lukeslaboratory/Stablebot-Core/STL's/Rear Z Plastic Peice.stl

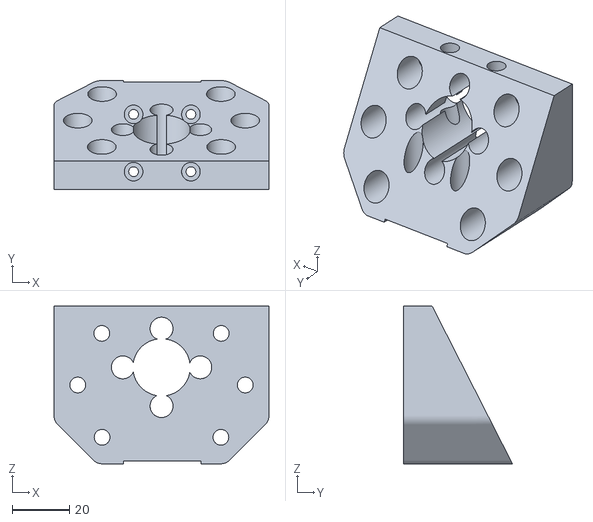
[picture p15: CAD file, 2021-12-18]
STL's/Rear Z Plastic Peice.stl
75.0 x 38.0 x 55.0
