lukeslaboratory/Stablebot-Core/STL's/Component449.3mf

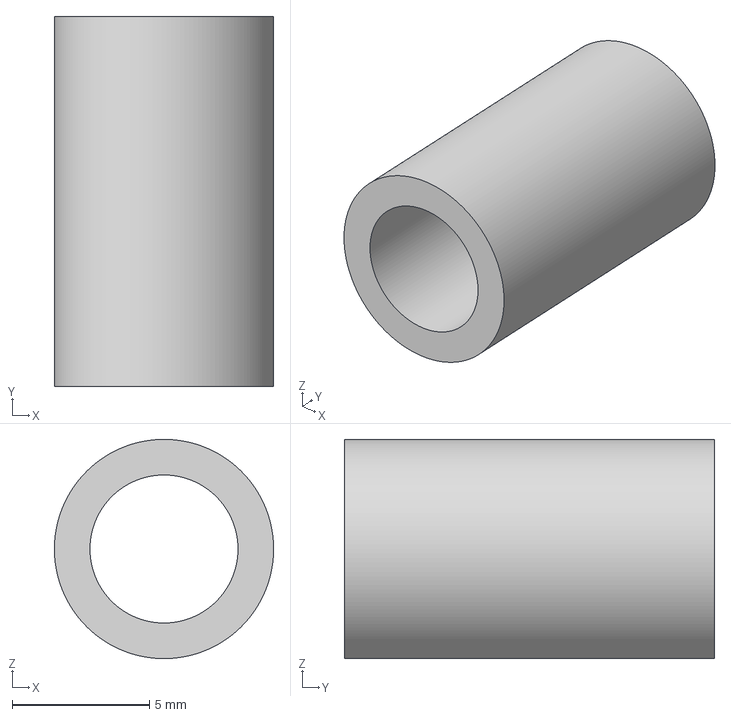
[picture p16: CAD file, 2021-12-18]
STL's/Component449.3mf
8.00 x 13.5 x 8.00 mm
