lukeslaboratory/Stablebot-Core/STL's/ToolPostBase.3mf

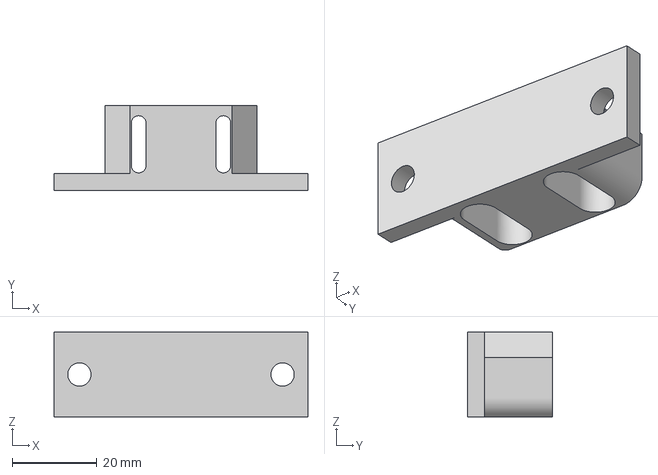
[picture p17: CAD file, 2021-12-18]
STL's/ToolPostBase.3mf
60.0 x 20.0 x 20.0 mm
