lukeslaboratory/Stablebot-Core/STL's/Plastic Base.3mf

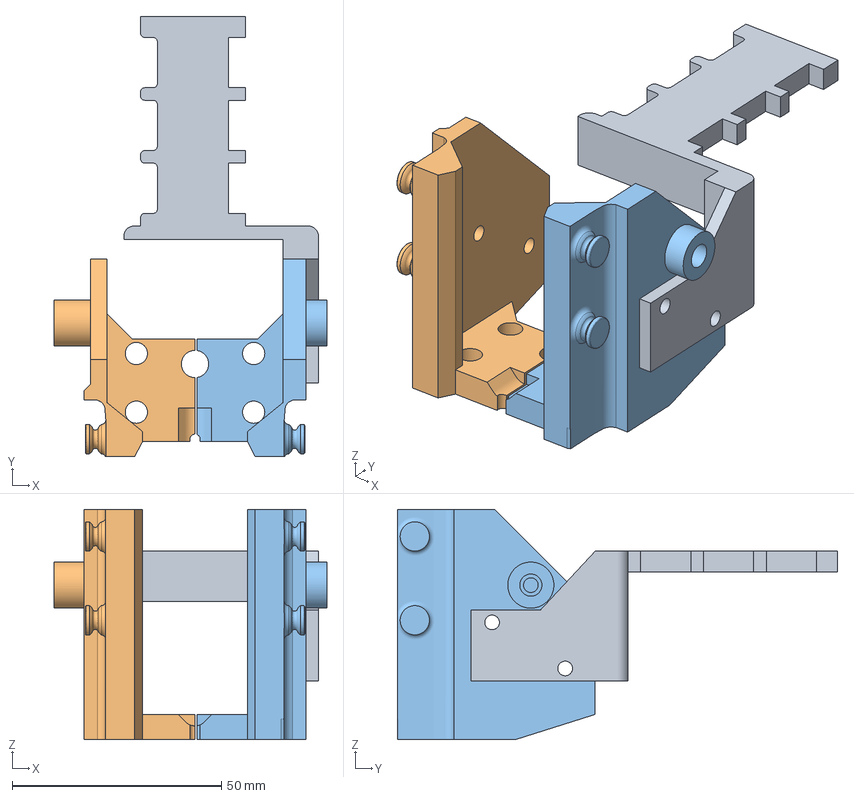
[picture p18: CAD file, 2021-12-18]
STL's/Plastic Base.3mf
65.2 x 105.0 x 55.0 mm
