lukeslaboratory/Stablebot-Core/STL's/Double_Shear_Rear.stl

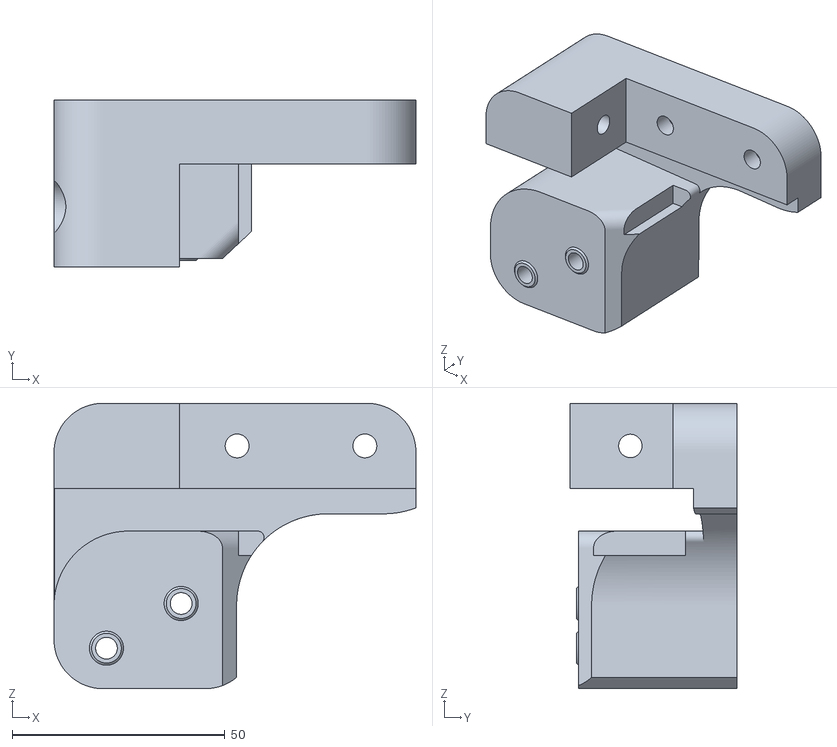
[picture p19: CAD file, 2021-12-18]
STL's/Double_Shear_Rear.stl
85.0 x 39.1 x 67.0
