lukeslaboratory/Stablebot-Core/STL's/Back Plate.3mf

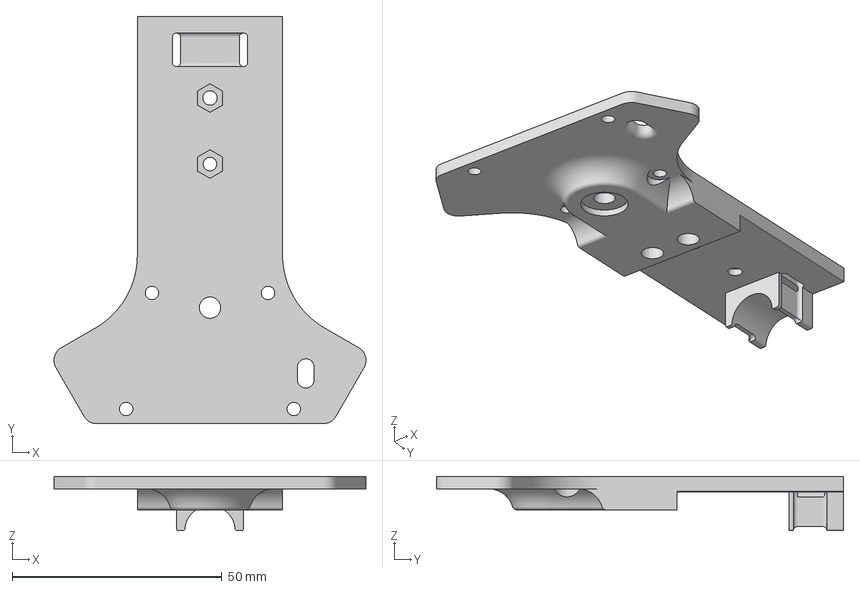
[picture p20: CAD file, 2021-12-18]
STL's/Back Plate.3mf
74.4 x 97.2 x 13.0 mm
