lukeslaboratory/Stablebot-Core/STL's/Belt_Motor_Tensioner.stl

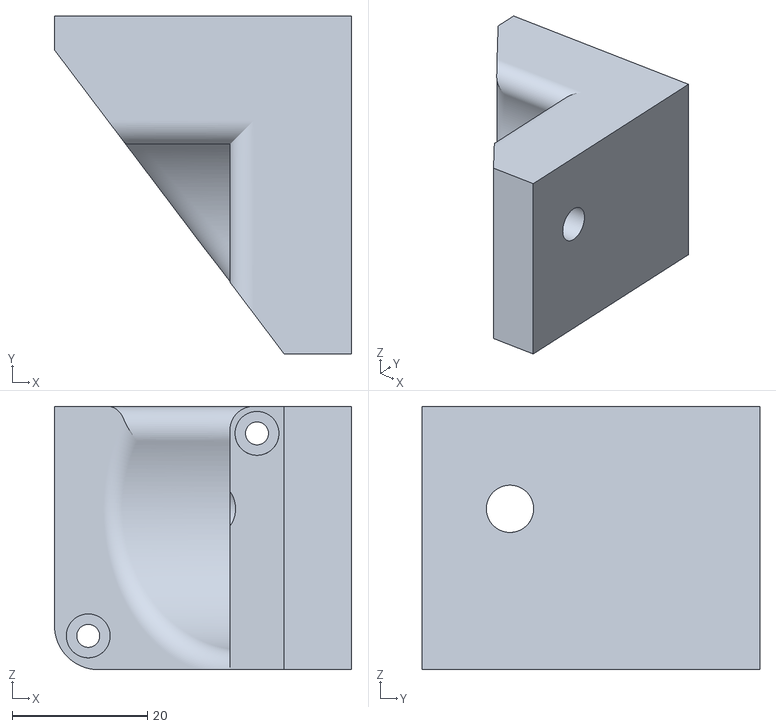
[picture p21: CAD file, 2021-12-18]
STL's/Belt_Motor_Tensioner.stl
44.0 x 50.0 x 39.0
