lukeslaboratory/Stablebot-Core/STL's/DoubleShear(Mirror).stl

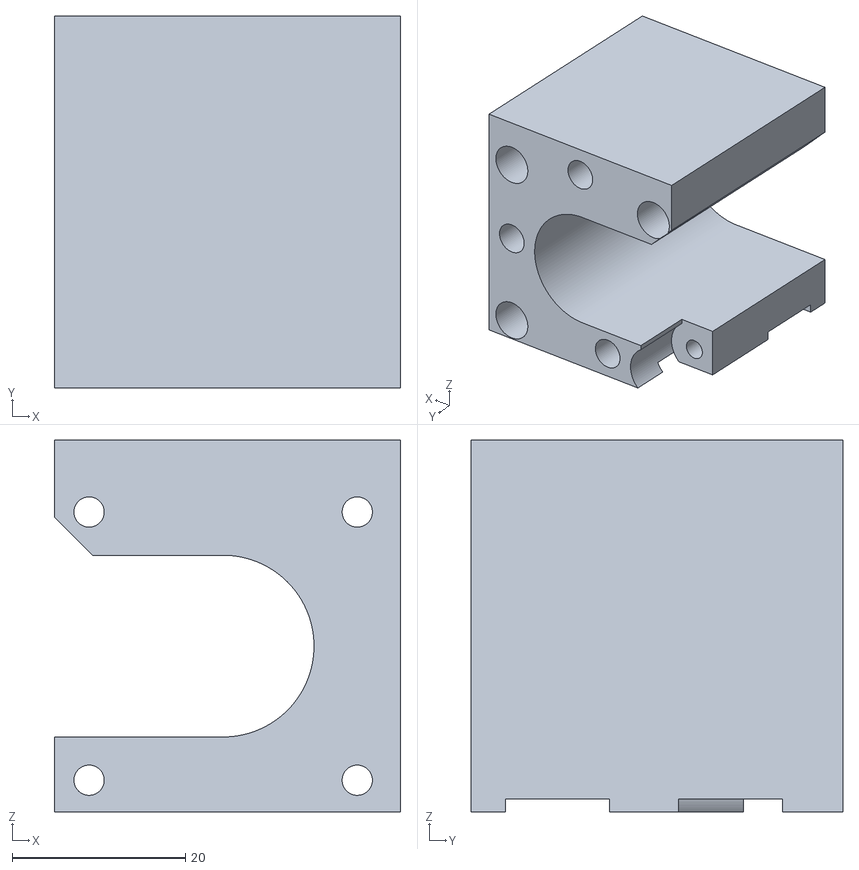
[picture p22: CAD file, 2021-12-18]
STL's/DoubleShear(Mirror).stl
40.0 x 43.0 x 43.0
