lukeslaboratory/Stablebot-Core/STL's/Internal Cablechain Handling.stl

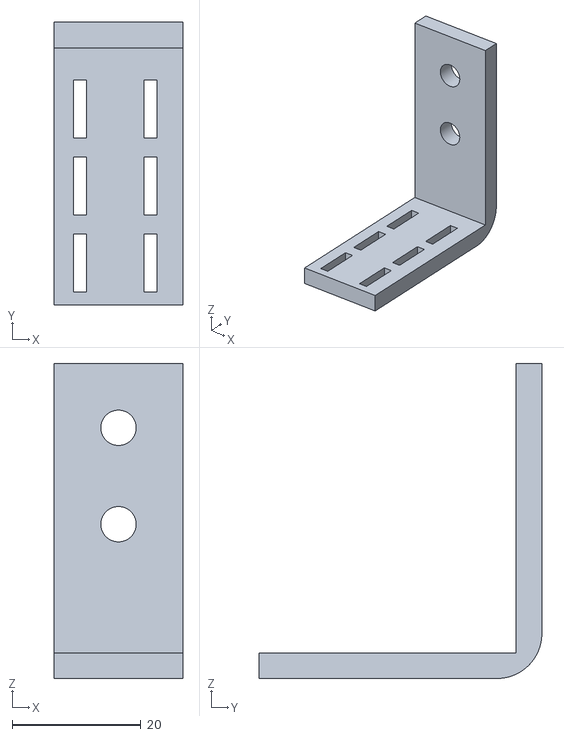
[picture p23: CAD file, 2021-12-18]
STL's/Internal Cablechain Handling.stl
20.0 x 44.0 x 49.0
