lukeslaboratory/Stablebot-Core/STL's/Gantry_Top_Support_StableBot Core v183_Body1_.stl

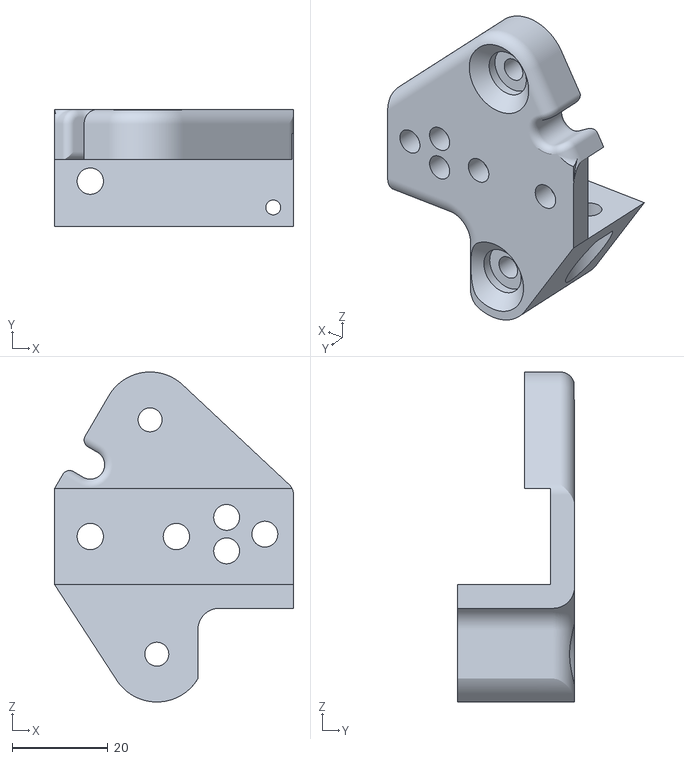
[picture p24: CAD file, 2021-12-18]
STL's/Gantry_Top_Support_StableBot Core v183_Body1_.stl
50.0 x 24.5 x 69.0
