lukeslaboratory/Stablebot-Core/STL's/Euclid Mount.3mf

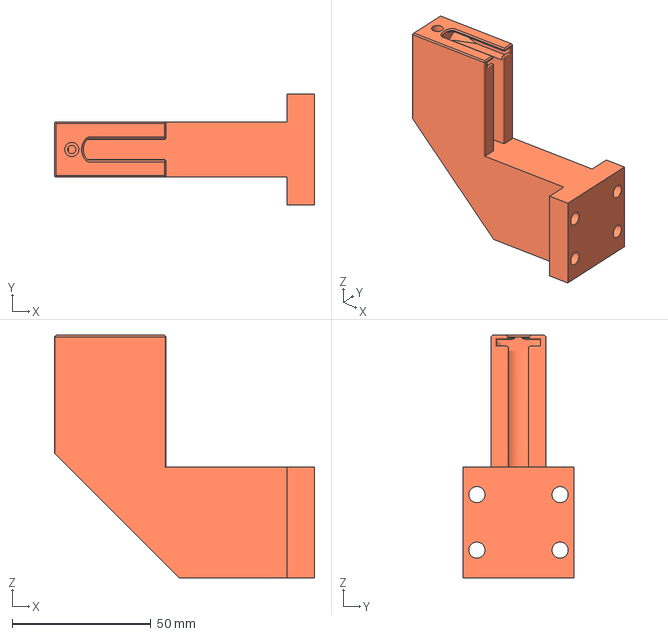
[picture p25: CAD file, 2021-12-18]
STL's/Euclid Mount.3mf
93.7 x 40.0 x 87.5 mm
