lukeslaboratory/Stablebot-Core/STL's/Attachment Front Z(Mirror).stl

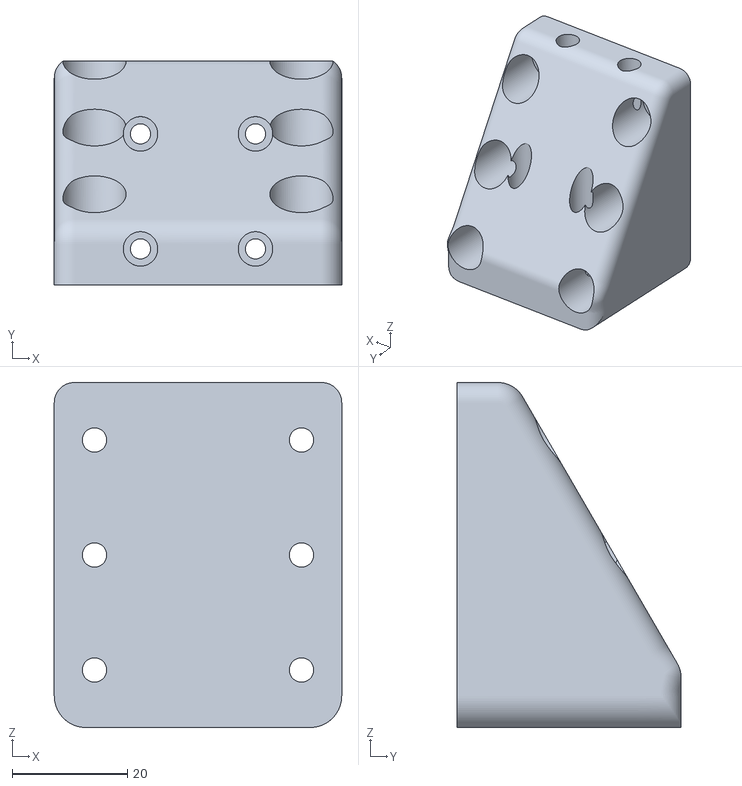
[picture p26: CAD file, 2021-12-18]
STL's/Attachment Front Z(Mirror).stl
50.0 x 39.0 x 60.0
