lukeslaboratory/Stablebot-Core/STL's/FrontBelt2.3mf

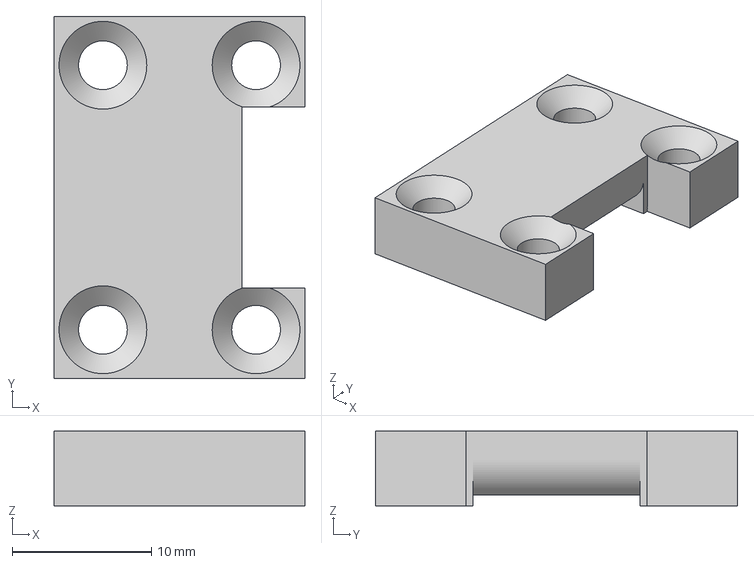
[picture p27: CAD file, 2021-12-18]
STL's/FrontBelt2.3mf
18.0 x 26.0 x 5.38 mm
