lukeslaboratory/Stablebot-Core/STL's/StableBot Core_ToolPostJub48 v2.3mf

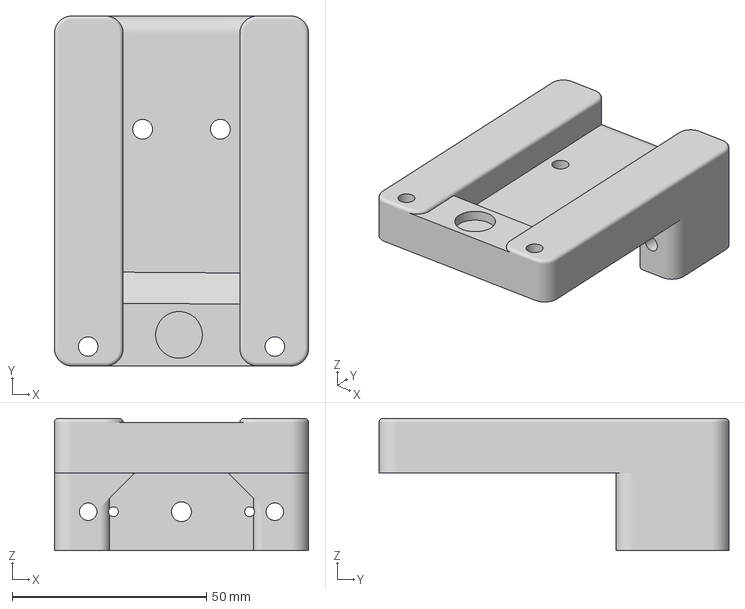
[picture p28: CAD file, 2021-12-18]
STL's/StableBot Core_ToolPostJub48 v2.3mf
65.4 x 90.0 x 34.0 mm
