lukeslaboratory/Stablebot-Core/STL's/beltclasp v1.3mf

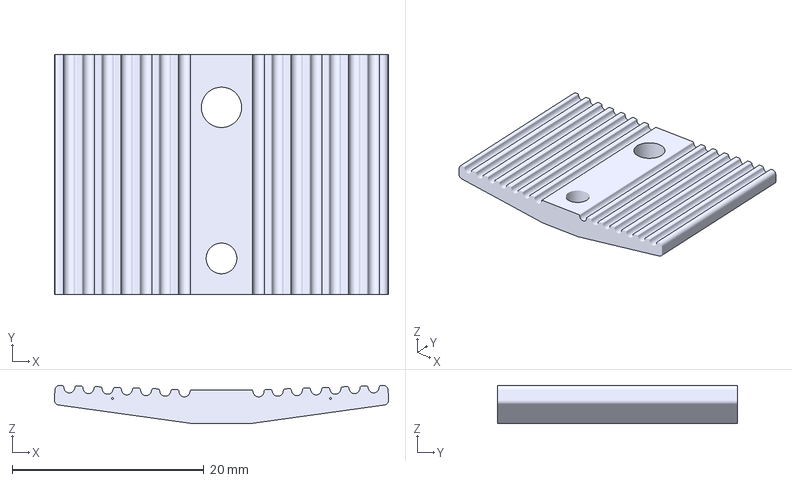
[picture p29: CAD file, 2021-12-18]
STL's/beltclasp v1.3mf
34.8 x 25.0 x 3.98 mm
