lukeslaboratory/Stablebot-Core/STL's/WAGO_DIN_2a.stl

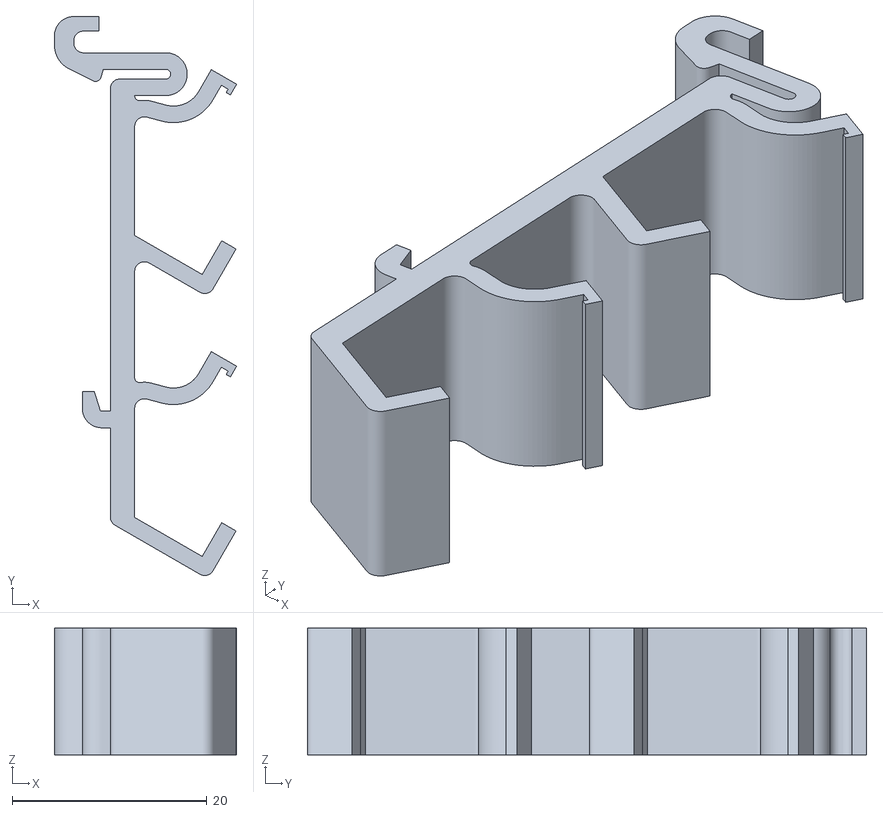
[picture p30: CAD file, 2021-12-18]
STL's/WAGO_DIN_2a.stl
18.7 x 57.4 x 13.0
