lukeslaboratory/Stablebot-Core/STL's/Plastic_Motor_Spacing.stl

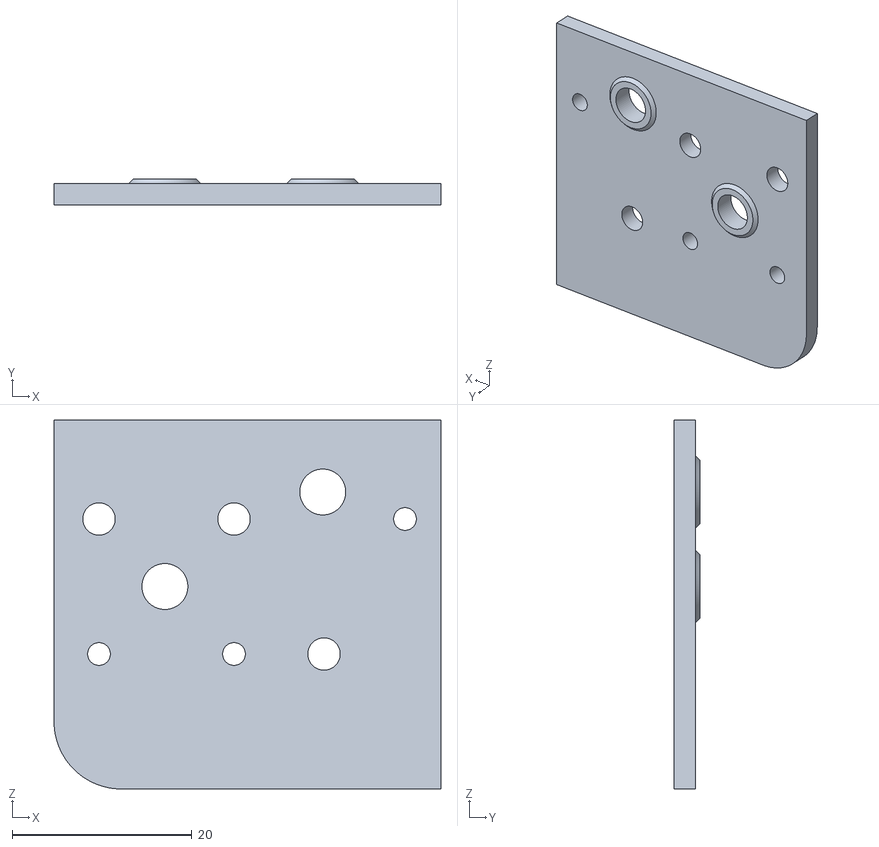
[picture p31: CAD file, 2021-12-18]
STL's/Plastic_Motor_Spacing.stl
43.0 x 2.90 x 41.0
