lukeslaboratory/Stablebot-Core/STL's/Transfer Plate Brace.stl

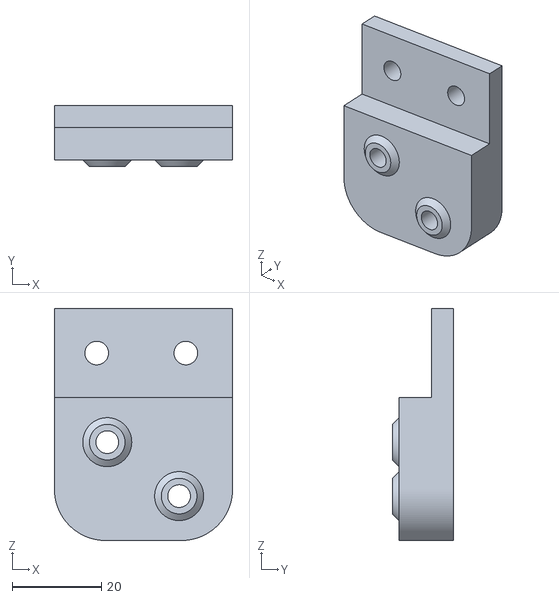
[picture p32: CAD file, 2021-12-18]
STL's/Transfer Plate Brace.stl
40.0 x 13.8 x 52.1
