lukeslaboratory/Stablebot-Core/STL's/Bearing Top.stl

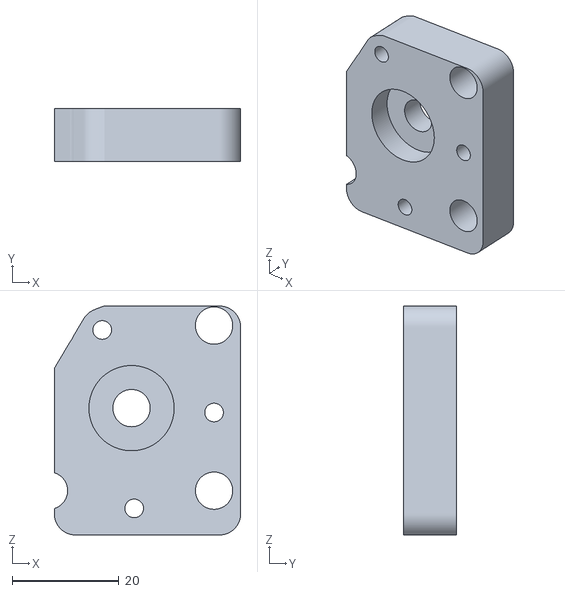
[picture p33: CAD file, 2021-12-18]
STL's/Bearing Top.stl
35.0 x 10.0 x 43.0
