lukeslaboratory/Stablebot-Core/STL's/Gantry_Top_Support(Mirror).stl

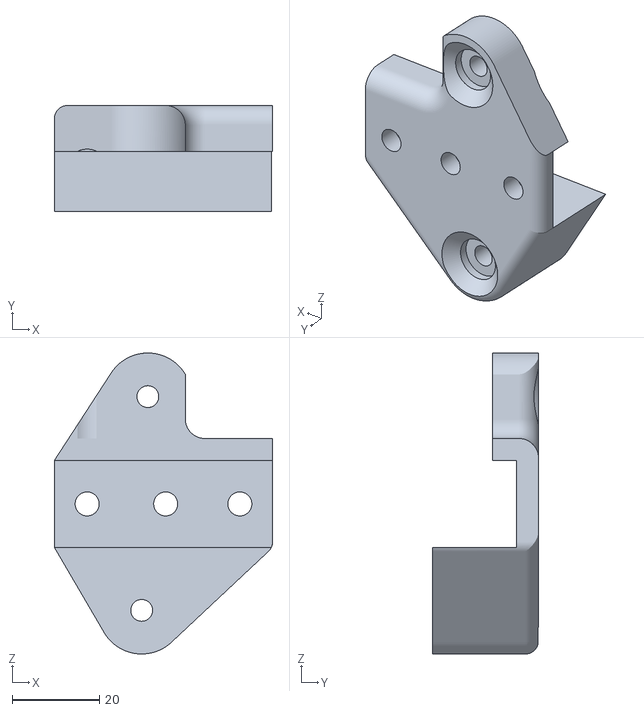
[picture p34: CAD file, 2021-12-18]
STL's/Gantry_Top_Support(Mirror).stl
50.0 x 24.3 x 69.0
