lukeslaboratory/Stablebot-Core/STL's/17.5mm standoff.3mf

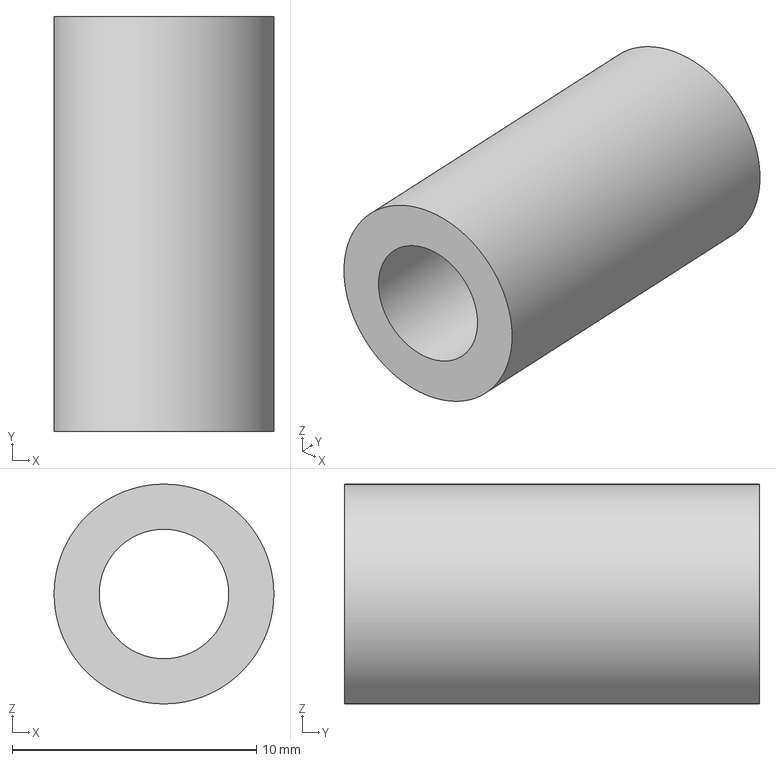
[picture p35: CAD file, 2021-12-18]
STL's/17.5mm standoff.3mf
9.00 x 17.0 x 9.00 mm
