lukeslaboratory/Stablebot-Core/STL's/Plastic_Motor_Spacing(Mirror).stl

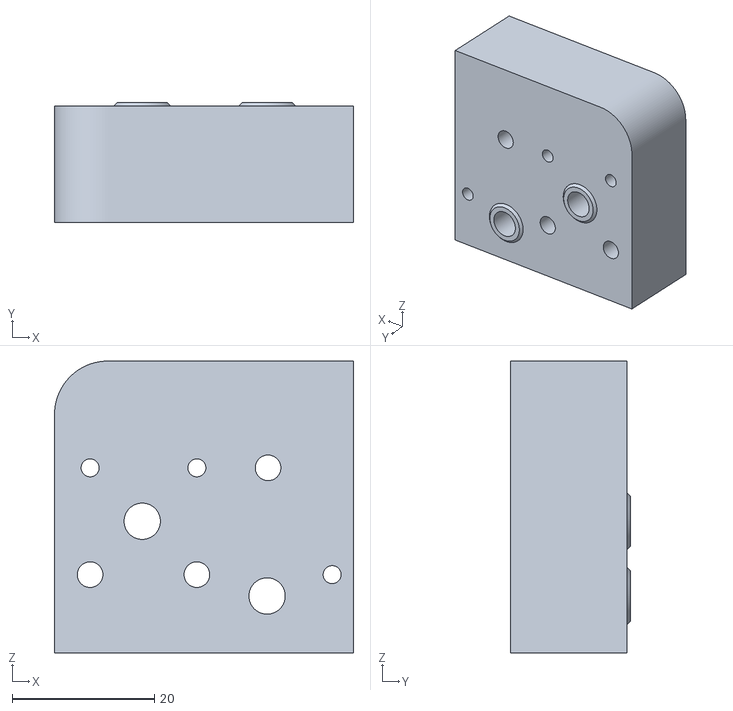
[picture p36: CAD file, 2021-12-18]
STL's/Plastic_Motor_Spacing(Mirror).stl
42.0 x 16.9 x 41.0
