lukeslaboratory/Stablebot-Core/STL's/Spacer+Standoff Plate.stl

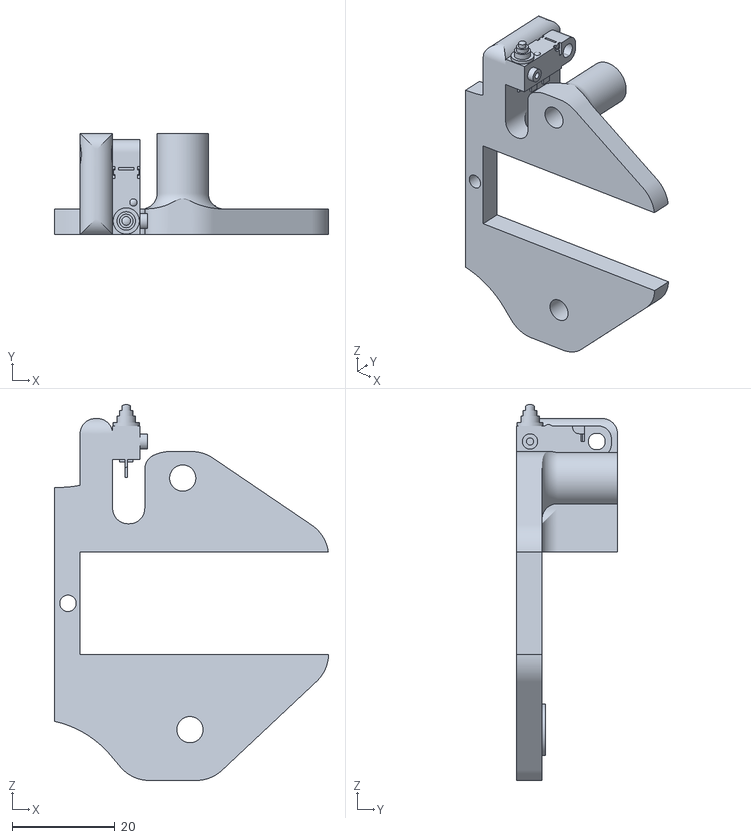
[picture p37: CAD file, 2021-12-18]
STL's/Spacer+Standoff Plate.stl
53.4 x 19.7 x 73.2
