lukeslaboratory/Stablebot-Core/STL's/Spacer+Standoff Plate(Mirror).stl

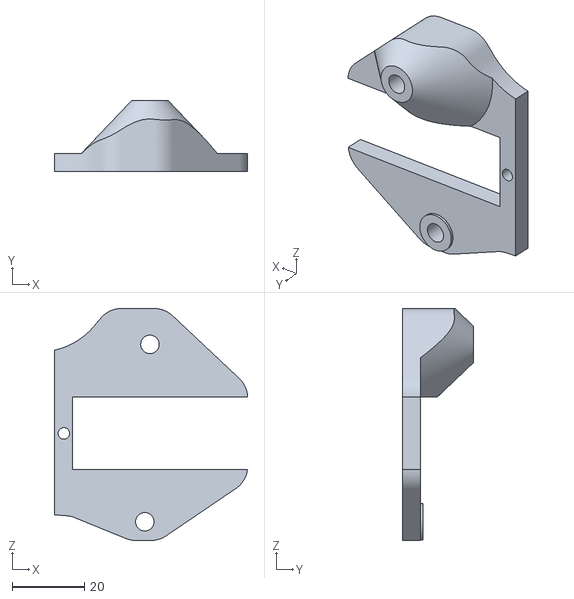
[picture p38: CAD file, 2021-12-18]
STL's/Spacer+Standoff Plate(Mirror).stl
53.4 x 19.7 x 64.1
