lukeslaboratory/Stablebot-Core/STL's/Orbiter_Slice_Tool Try 2_Probe_Holder_Euclid v1.3mf

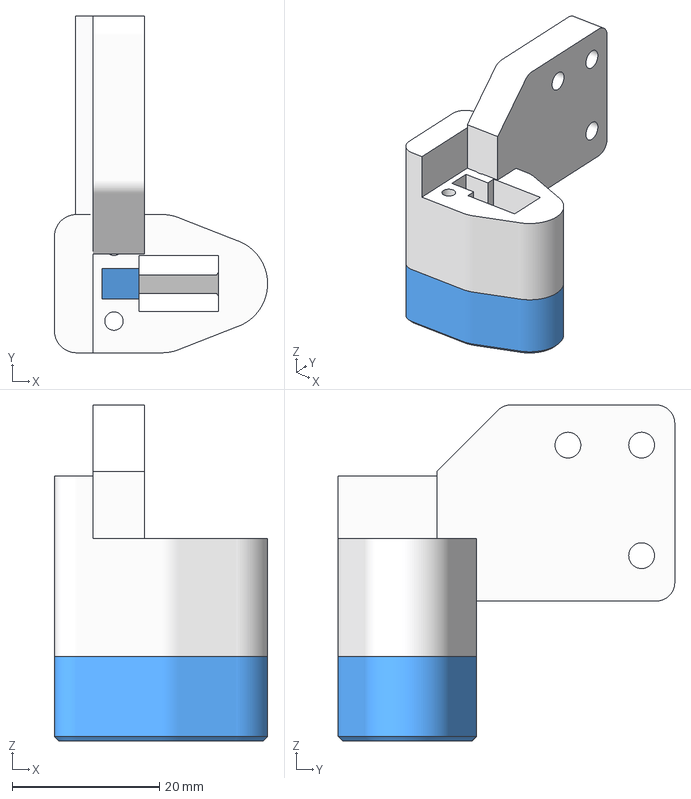
[picture p39: CAD file, 2021-12-18]
STL's/Orbiter_Slice_Tool Try 2_Probe_Holder_Euclid v1.3mf
28.9 x 45.7 x 45.6 mm
