lukeslaboratory/Stablebot-Core/STL's/TopPlateREL.3mf

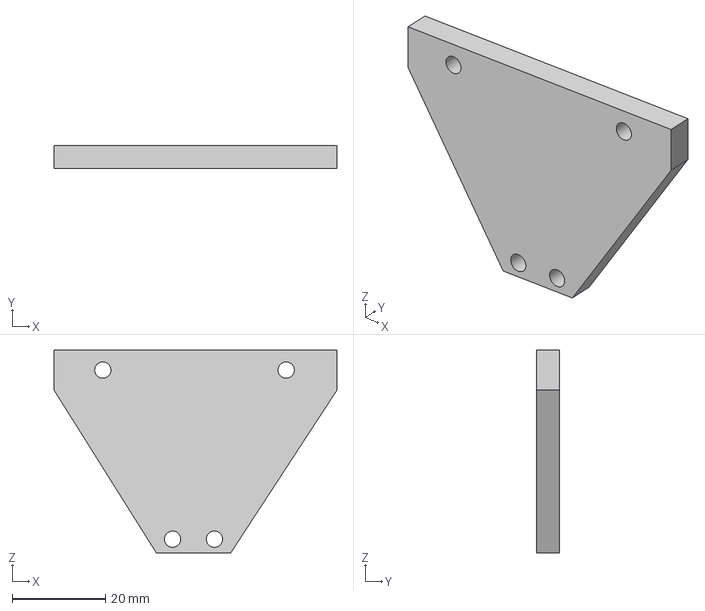
[picture p40: CAD file, 2021-12-18]
STL's/TopPlateREL.3mf
60.9 x 5.00 x 43.6 mm
