lukeslaboratory/Stablebot-Core/STL's/Front_Belt_1.3mf

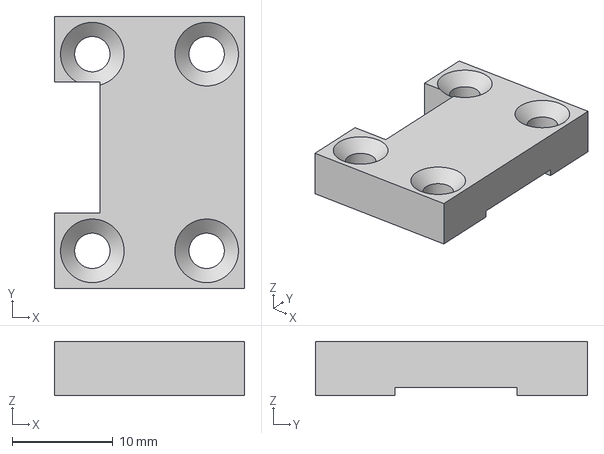
[picture p41: CAD file, 2021-12-18]
STL's/Front_Belt_1.3mf
18.8 x 27.0 x 5.38 mm
