lukeslaboratory/Stablebot-Core/STL's/Gantry_Top_Support_StableBot Core v183_Body2_.stl

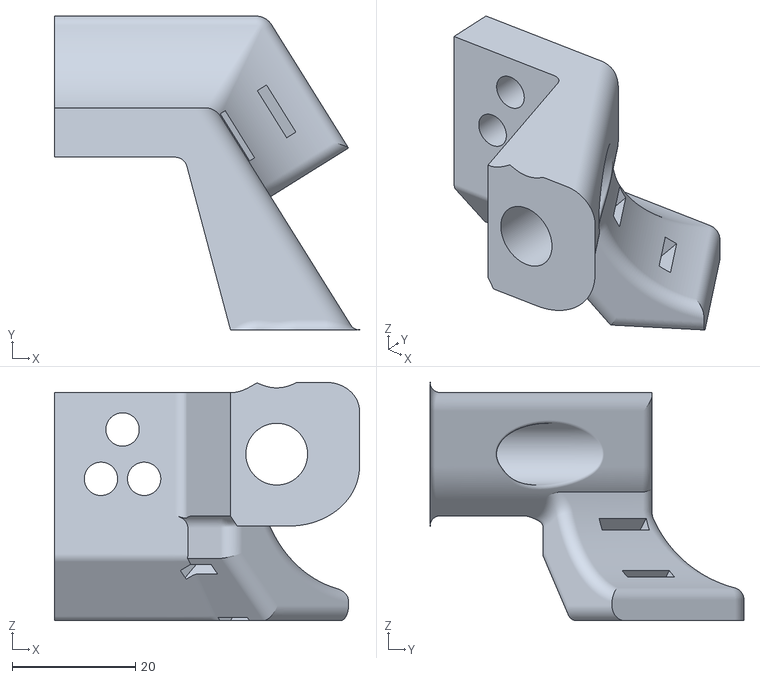
[picture p42: CAD file, 2021-12-18]
STL's/Gantry_Top_Support_StableBot Core v183_Body2_.stl
49.4 x 50.9 x 38.6
