lukeslaboratory/Stablebot-Core/STL's/3mm Standoff.3mf

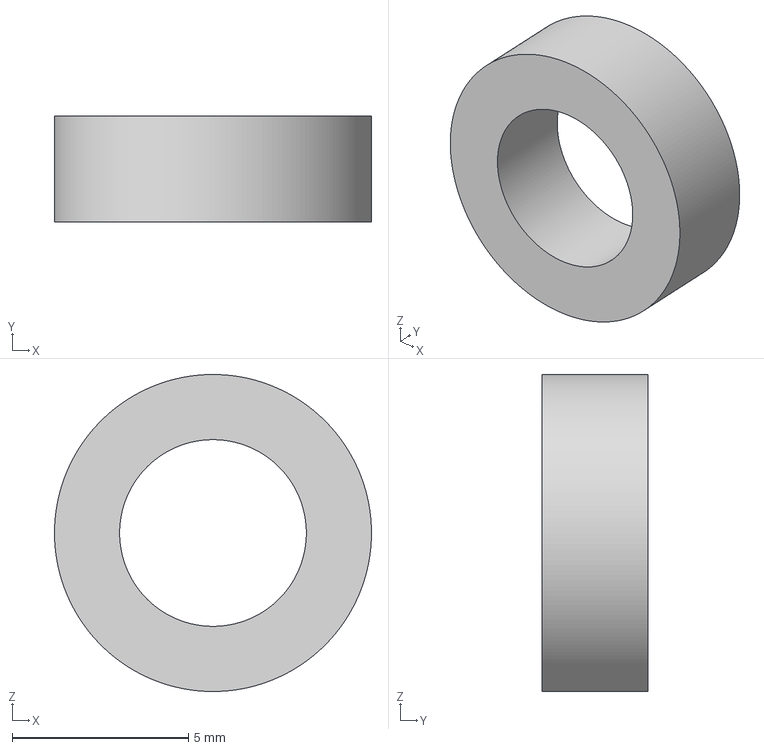
[picture p43: CAD file, 2021-12-18]
STL's/3mm Standoff.3mf
9.00 x 3.00 x 9.00 mm
